Rowlhouse/bandonino/Bandonino/Bitmaps.h

#ifndef BITMAPS_H
#define BITMAPS_H
#include <stdint.h>

// https://mischianti.org/images-to-byte-array-online-converter-cpp-arduino/

static const uint16_t NoteHeadSize[] = {8, 7};
static const int NoteHeadOffsets[] = {-4, -4};

// Offsets are from the note position
static const uint16_t SharpSize[] = {6, 15};
static const int SharpOffsets[] = {-13, -8};

// Offsets are from the note position
static const uint16_t FlatSize[] = {5,12};
static const int FlatOffsets[] = {-12, -4};

// 'NoteHeadLine', 8x7px
static const unsigned char NoteHeadLine [] = {
	0x1c, 0x7e, 0xff, 0x00, 0xff, 0x7e, 0x38
};
// 'NoteHeadSpace', 8x7px
static const unsigned char NoteHeadSpace [] = {
	0x1c, 0x7e, 0xff, 0xff, 0xff, 0x7e, 0x38
};

static const unsigned char SharpSpace [] = {
	// 'SharpSpace, 6x15px
	0x08, 0x08, 0x48, 0x4c, 0x5c, 0x78, 0xe8, 0xcc, 0x5c, 0x78, 0xe8, 0xc8, 0x48, 0x40, 0x40
};

// 'FlatSpace', 5x12px
static const unsigned char FlatSpace [] = {
	0x80, 0x80, 0x80, 0x80, 0x80, 0xb0, 0xc8, 0x88, 0x88, 0x90, 0xa0, 0xc0
};

// 'ClefPage', 128x128px
static const unsigned char ClefPage [] = {
	0x00, 0x00, 0x00, 0x00, 0x00, 0x00, 0x00, 0x00, 0x00, 0x00, 0x00, 0x00, 0x00, 0x00, 0x00, 0x00, 
	0x00, 0x00, 0x00, 0x00, 0x00, 0x00, 0x00, 0x00, 0x00, 0x00, 0x00, 0x00, 0x00, 0x00, 0x00, 0x00, 
	0x00, 0x00, 0x00, 0x00, 0x00, 0x00, 0x00, 0x00, 0x00, 0x00, 0x00, 0x00, 0x00, 0x00, 0x00, 0x00, 
	0x00, 0x00, 0x00, 0x00, 0x00, 0x00, 0x00, 0x00, 0x00, 0x00, 0x00, 0x00, 0x00, 0x00, 0x00, 0x00, 
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
	0x00, 0x00, 0x00, 0x00, 0x00, 0x00, 0x00, 0x00, 0x00, 0x00, 0x00, 0x00, 0x00, 0x00, 0x00, 0x00, 
	0x00, 0x00, 0x00, 0x00, 0x00, 0x00, 0x00, 0x00, 0x00, 0x00, 0x00, 0x00, 0x00, 0x00, 0x00, 0x00, 
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
};


#endif
