Rowlhouse/bandonino/Bandonino/NoteNames.h

#ifndef NOTENAMES_H
#define NOTENAMES_H

// MIDI pitch values. 00 means unused
// Midle C is in octave 5
#define NOTE_CN 0
#define NOTE_CS 1
#define NOTE_DN 2
#define NOTE_DS 3
#define NOTE_EN 4
#define NOTE_FN 5
#define NOTE_FS 6
#define NOTE_GN 7
#define NOTE_GS 8
#define NOTE_AN 9
#define NOTE_AS 10
#define NOTE_BN 11

#define NOTE(note, octave) (12 + octave * 12 + NOTE_##note)
#define NOTE_UNUSED 0
#define SKIPPED_KEY 0
#define NOTE_BUTTON 0

enum AccidentalPreference {
  ACCIDENTAL_PREFERENCE_SHARP,
  ACCIDENTAL_PREFERENCE_FLAT,
  ACCIDENTAL_PREFERENCE_KEY
};

extern const char* gAccidentalPreferenceNames[];

constexpr int NUM_KEYS = 11;
constexpr int KEY_OFFSET = 5; // for middle C
extern const char* gKeyNames[NUM_KEYS];

enum Clef {
  CLEF_BASS,
  CLEF_TREBLE
};

struct NoteInfo {
  NoteInfo(int stavePosition = 0, int accidental = 0)
    : mStavePosition(stavePosition), mAccidental(accidental) {}
  int mStavePosition = 0;
  int mAccidental = 0;
  int mNote = 0;
  int mOctave = 0;
  char mName[16] = {'\0'};
};

NoteInfo getNoteInfo(int midiNote, int clef, int accidentalPreference, int accidentalKey);

#endif
